SyWier/Bidirectional-Power-Supply/Altium/UPS/ALTIUM_EMBEDDED_MODELS/MLZ1608E100MT.stp

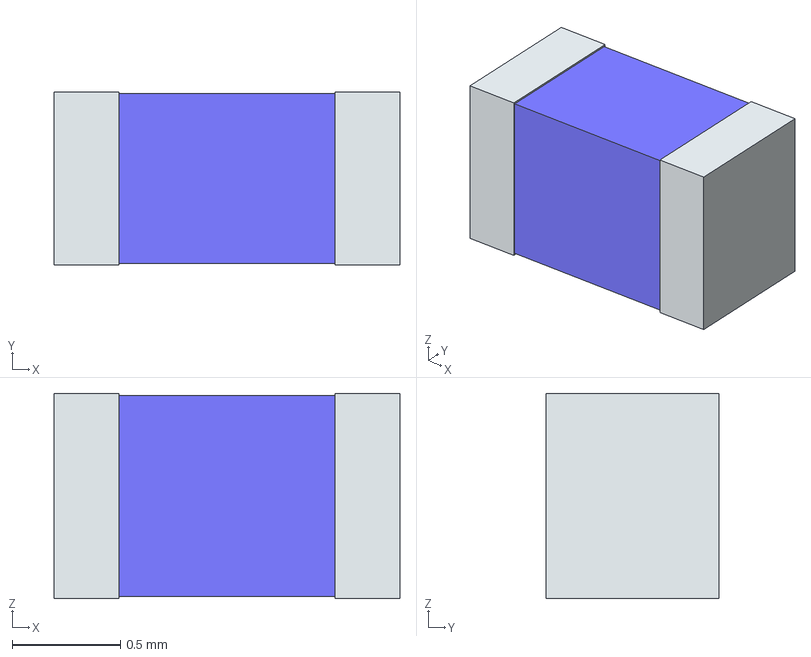
[picture p31: CAD file, 2024-12-01]
Altium/UPS/ALTIUM_EMBEDDED_MODELS/MLZ1608E100MT.stp
1.60 x 0.8 x 0.95 mm
term1
term2
