SyWier/Bidirectional-Power-Supply/Altium/UPS/ALTIUM_EMBEDDED_MODELS/H-LEAD_D10_L12.5__GAS-ESCAPE-RUBBER_COATED-CASE_STRUCTURE.stp

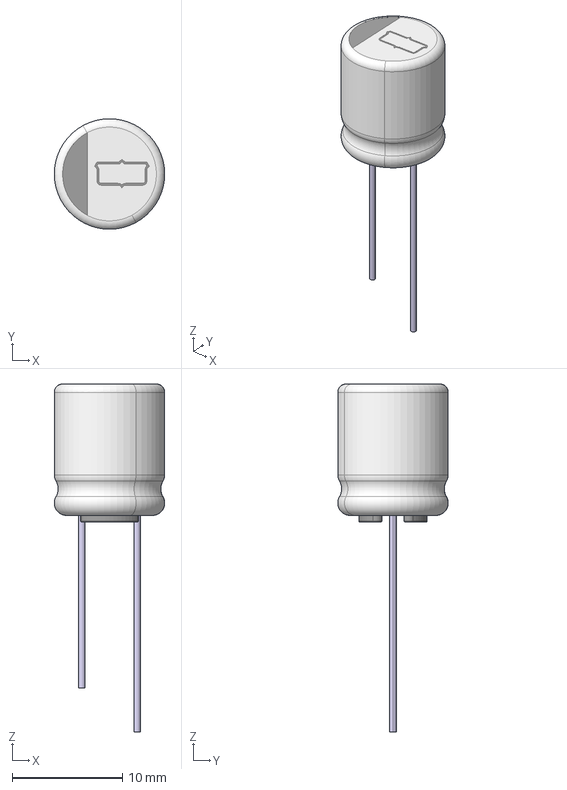
[picture p32: CAD file, 2024-12-01]
Altium/UPS/ALTIUM_EMBEDDED_MODELS/H-LEAD_D10_L12.5__GAS-ESCAPE-RUBBER_COATED-CASE_STRUCTURE.stp
10.00 x 10.00 x 31.5 mm
H-LEAD_D10_TERMINAL+
H-LEAD_D10_TERMINAL-
H-LEAD_D10_L12.5_ELEMENT
