SyWier/Bidirectional-Power-Supply/Altium/UPS/ALTIUM_EMBEDDED_MODELS/LVT12R0050FER.stp

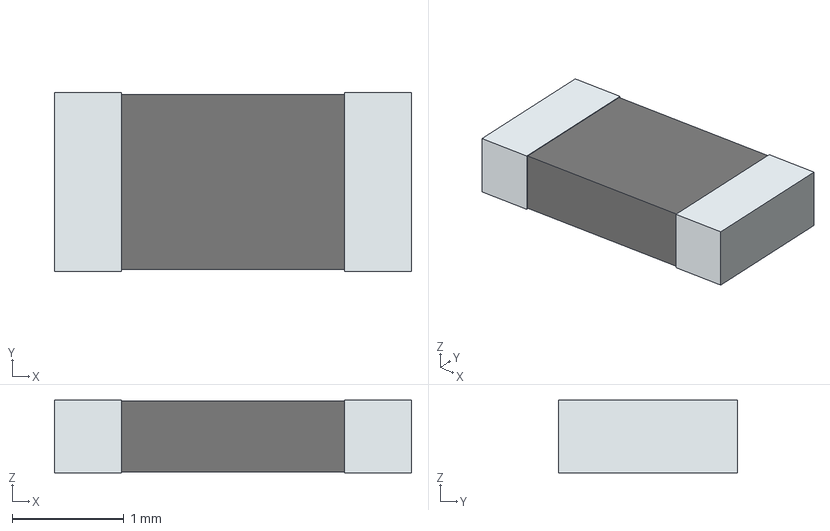
[picture p33: CAD file, 2024-12-01]
Altium/UPS/ALTIUM_EMBEDDED_MODELS/LVT12R0050FER.stp
3.20 x 1.60 x 0.65 mm
term1
term2
