SyWier/Bidirectional-Power-Supply/Altium/UPS/ALTIUM_EMBEDDED_MODELS/PTS526_SMG15J_SMTR2_LFS.stp

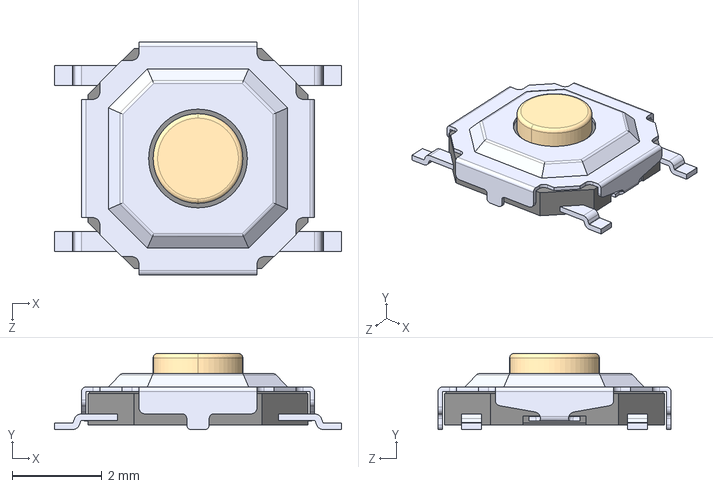
[picture p34: CAD file, 2024-12-01]
Altium/UPS/ALTIUM_EMBEDDED_MODELS/PTS526_SMG15J_SMTR2_LFS.stp
6.40 x 1.70 x 5.20 mm
