SyWier/Bidirectional-Power-Supply/Altium/UPS/ALTIUM_EMBEDDED_MODELS/CP2102N-A02-GQFN20R.stp

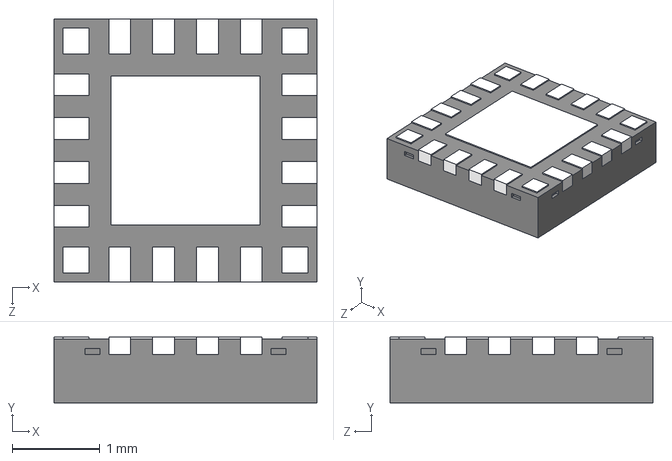
[picture p35: CAD file, 2024-12-01]
Altium/UPS/ALTIUM_EMBEDDED_MODELS/CP2102N-A02-GQFN20R.stp
3.00 x 0.75 x 3.00 mm
