SyWier/Bidirectional-Power-Supply/Altium/UPS/ALTIUM_EMBEDDED_MODELS/TPS2116DRLR.stp

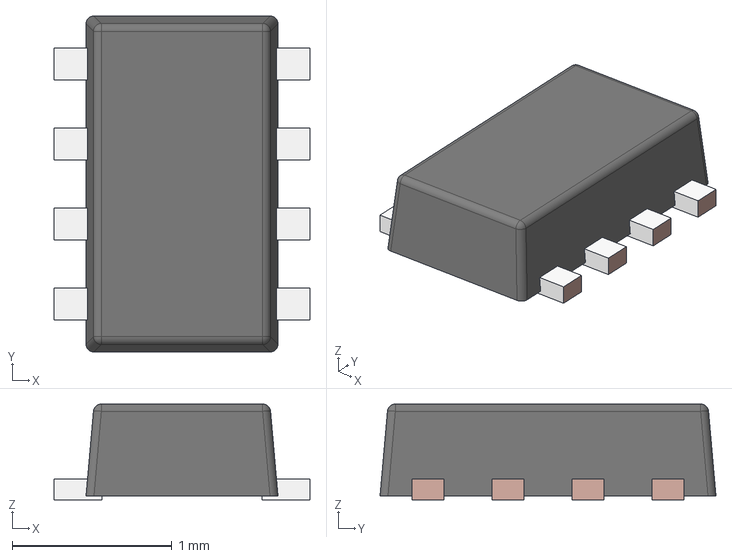
[picture p36: CAD file, 2024-12-01]
Altium/UPS/ALTIUM_EMBEDDED_MODELS/TPS2116DRLR.stp
1.60 x 2.10 x 0.6 mm
FRAME-DRL0008A
BODY-SOT
