SyWier/Bidirectional-Power-Supply/Altium/UPS/ALTIUM_EMBEDDED_MODELS/PHT0603Y1001FGW.stp

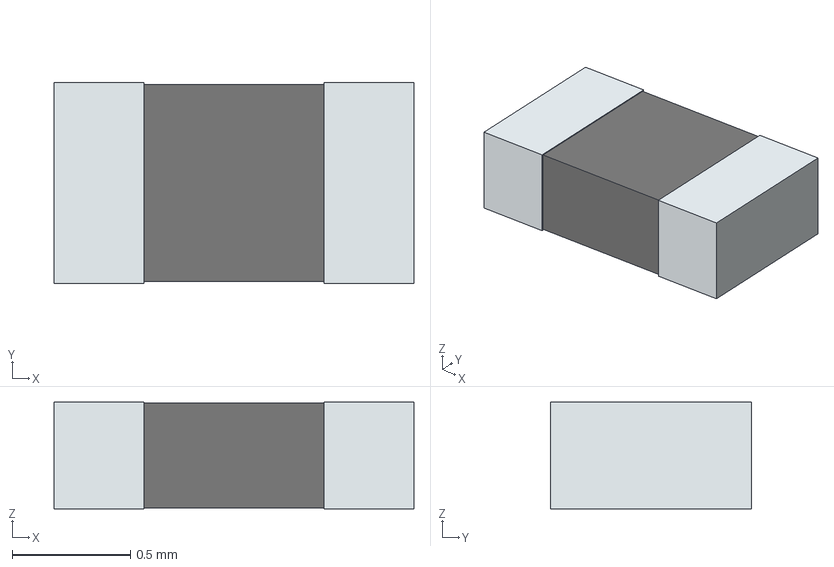
[picture p37: CAD file, 2024-12-01]
Altium/UPS/ALTIUM_EMBEDDED_MODELS/PHT0603Y1001FGW.stp
1.52 x 0.85 x 0.451 mm
term1
term2
