SyWier/Bidirectional-Power-Supply/Altium/UPS/ALTIUM_EMBEDDED_MODELS/MCP6C04T-020E_CHY.stp

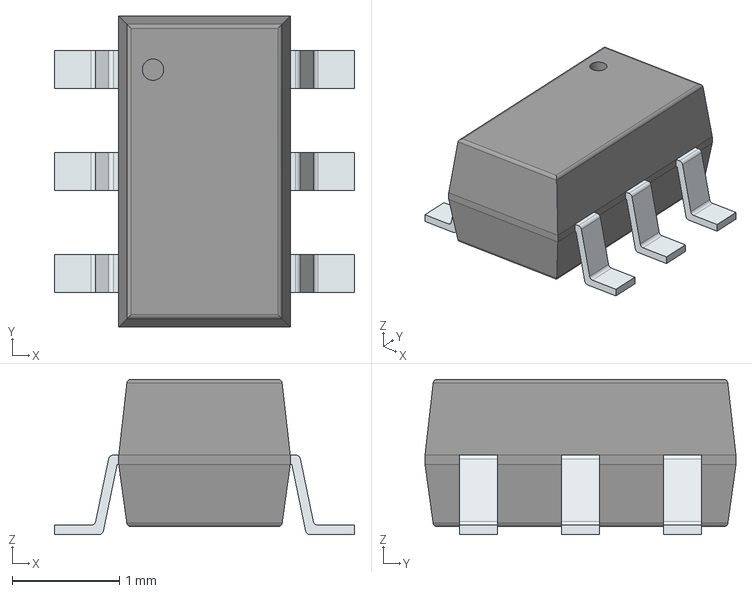
[picture p38: CAD file, 2024-12-01]
Altium/UPS/ALTIUM_EMBEDDED_MODELS/MCP6C04T-020E_CHY.stp
2.80 x 2.90 x 1.45 mm
PinsArrayLR
