SyWier/Bidirectional-Power-Supply/Altium/UPS/ALTIUM_EMBEDDED_MODELS/VS-MBRS130L-M3_5BT.stp

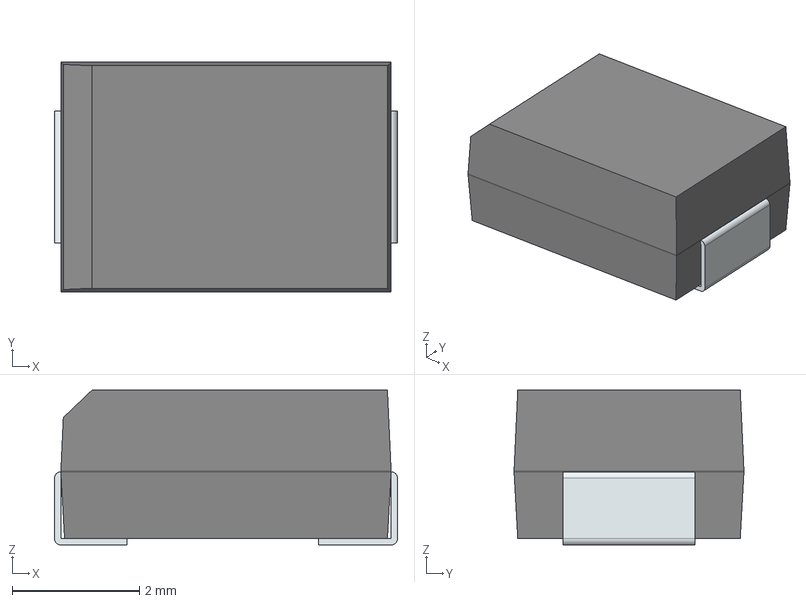
[picture p39: CAD file, 2024-12-01]
Altium/UPS/ALTIUM_EMBEDDED_MODELS/VS-MBRS130L-M3_5BT.stp
5.40 x 3.62 x 2.44 mm
FilletPin1
FilletPin2
