SyWier/Bidirectional-Power-Supply/Altium/UPS/ALTIUM_EMBEDDED_MODELS/ECH8695R-TL-W.stp

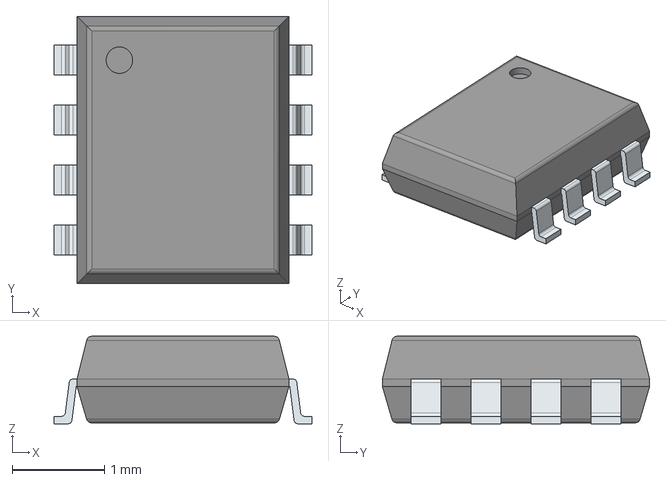
[picture p40: CAD file, 2024-12-01]
Altium/UPS/ALTIUM_EMBEDDED_MODELS/ECH8695R-TL-W.stp
2.80 x 2.90 x 0.95 mm
PinsArrayLR
