SyWier/Bidirectional-Power-Supply/Altium/UPS/ALTIUM_EMBEDDED_MODELS/LP5907QMFX-3.3Q1.stp

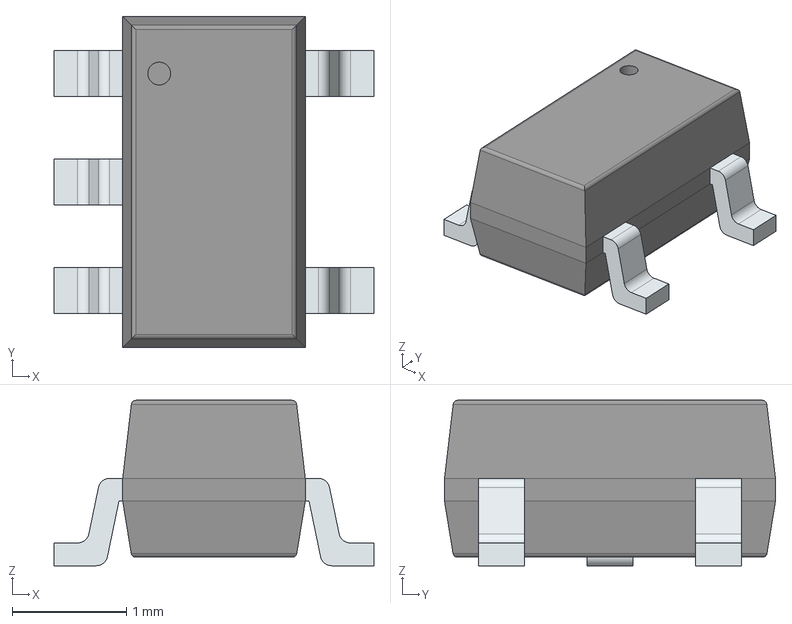
[picture p41: CAD file, 2024-12-01]
Altium/UPS/ALTIUM_EMBEDDED_MODELS/LP5907QMFX-3.3Q1.stp
2.80 x 2.90 x 1.45 mm
PinsArrayL
PinsArrayR
