SyWier/Bidirectional-Power-Supply/Altium/UPS/ALTIUM_EMBEDDED_MODELS/SS-52100-001.stp

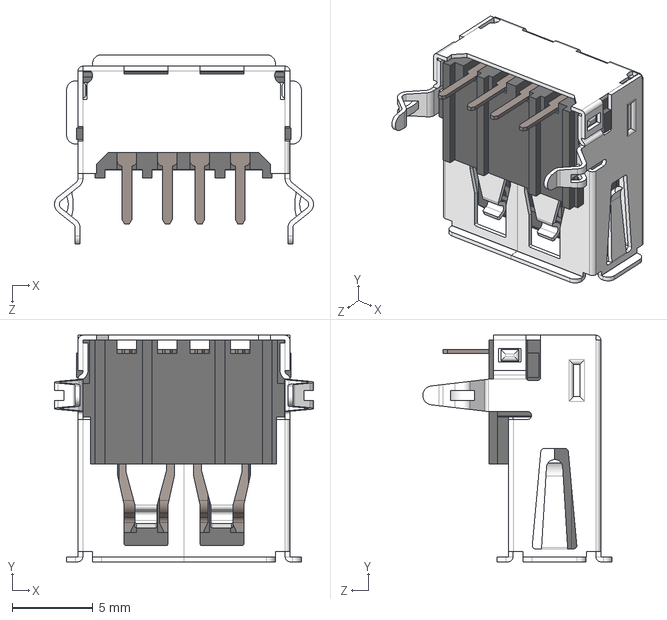
[picture p42: CAD file, 2024-12-01]
Altium/UPS/ALTIUM_EMBEDDED_MODELS/SS-52100-001.stp
16.0 x 14.0 x 11.7 mm
