SyWier/Bidirectional-Power-Supply/Altium/UPS/ALTIUM_EMBEDDED_MODELS/FTSH-105-01-L-DV-K.stp

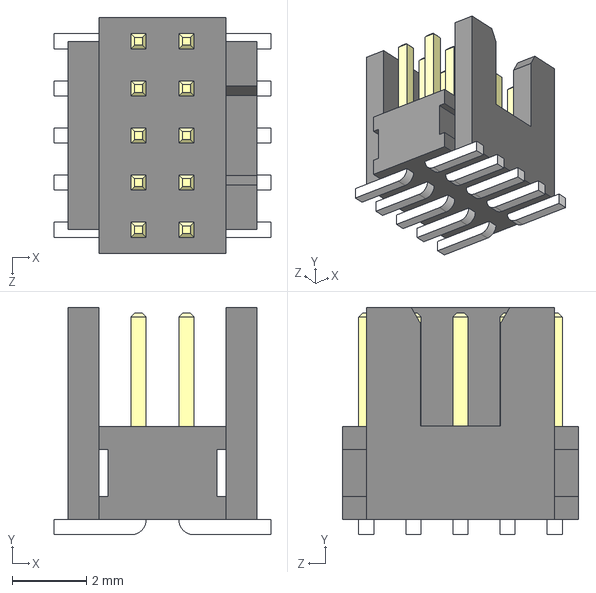
[picture p43: CAD file, 2024-12-01]
Altium/UPS/ALTIUM_EMBEDDED_MODELS/FTSH-105-01-L-DV-K.stp
5.85 x 6.13 x 6.35 mm
