SyWier/Bidirectional-Power-Supply/Altium/UPS/ALTIUM_EMBEDDED_MODELS/USB-B.STEP

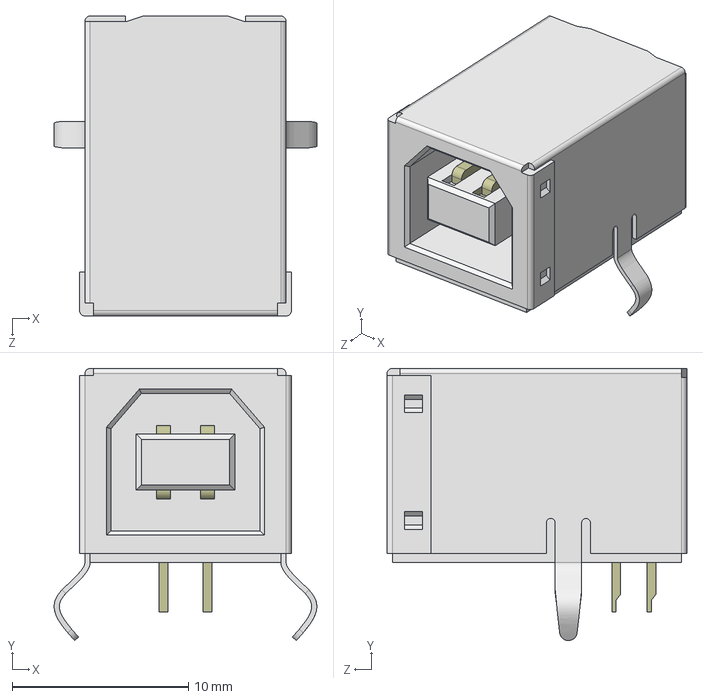
[picture p44: CAD file, 2024-12-01]
Altium/UPS/ALTIUM_EMBEDDED_MODELS/USB-B.STEP
14.9 x 15.4 x 17.0 mm
