SyWier/Bidirectional-Power-Supply/Altium/UPS/ALTIUM_EMBEDDED_MODELS/ESDAULC6-3BP6.stp

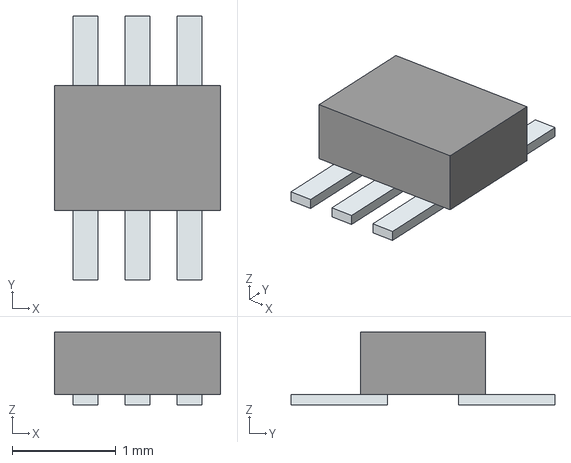
[picture p45: CAD file, 2024-12-01]
Altium/UPS/ALTIUM_EMBEDDED_MODELS/ESDAULC6-3BP6.stp
1.60 x 2.54 x 0.7 mm
Pins
