SyWier/Bidirectional-Power-Supply/CSS/Tools/HiTerm/HiTerm.ini

PORT=COM12
MON_POS=49,635
REN_POS=108,100
WATCHWINDOW_POS=1,0,5,0,0,0,0,0
SETTINGS=2,5,1,2000,10,1,256,0,5,1234,1,40,0,57600
REC_POS_0=30,45
REC_TRIGGER_0_A=0,0,0,1,1
RECTAB_NAME_0_A=Basic
REC_VAR_0_A_0=,1,1000,0,1,1
REC_VAR_0_A_1=,1,1000,0,1,1
REC_VAR_0_A_2=,1,1000,0,1,1
REC_VAR_0_A_3=,1,1000,0,1,1
REC_TRIGGER_0_B=0,0,0,1,1
RECTAB_NAME_0_B=Development
REC_VAR_0_B_0=,1,1000,0,1,1
REC_VAR_0_B_1=,1,1000,0,1,1
REC_VAR_0_B_2=,1,1000,0,1,1
REC_VAR_0_B_3=,1,1000,0,1,1
REC_TRIGGER_0_C=0,0,0,1,1
RECTAB_NAME_0_C=General
REC_VAR_0_C_0=,1,1000,0,1,1
REC_VAR_0_C_1=,1,1000,0,1,1
REC_VAR_0_C_2=,1,1000,0,1,1
REC_VAR_0_C_3=,1,1000,0,1,1
REC_TRIGGER_0_D=0,0,0,1,1
RECTAB_NAME_0_D=Whatever
REC_VAR_0_D_0=,1,1000,0,1,1
REC_VAR_0_D_1=,1,1000,0,1,1
REC_VAR_0_D_2=,1,1000,0,1,1
REC_VAR_0_D_3=,1,1000,0,1,1
REC_TRIGGER_0_E=0,0,0,1,1
RECTAB_NAME_0_E=DbgOsc - 1
REC_VAR_0_E_0=,1,1000,0,1,1
REC_VAR_0_E_1=,1,1000,0,1,1
REC_VAR_0_E_2=,1,1000,0,1,1
REC_VAR_0_E_3=,1,1000,0,1,1
REC_TRIGGER_0_F=0,0,0,1,1
RECTAB_NAME_0_F=DbgOsc - 2
REC_VAR_0_F_0=,1,1000,0,1,1
REC_VAR_0_F_1=,1,1000,0,1,1
REC_VAR_0_F_2=,1,1000,0,1,1
REC_VAR_0_F_3=,1,1000,0,1,1
REC_TRIGGER_0_G=0,0,0,1,1
RECTAB_NAME_0_G=DbgOsc - 3
REC_VAR_0_G_0=,1,1000,0,1,1
REC_VAR_0_G_1=,1,1000,0,1,1
REC_VAR_0_G_2=,1,1000,0,1,1
REC_VAR_0_G_3=,1,1000,0,1,1
REC_TRIGGER_0_H=0,0,0,1,1
RECTAB_NAME_0_H=DbgOsc - 4
REC_VAR_0_H_0=,1,1000,0,1,1
REC_VAR_0_H_1=,1,1000,0,1,1
REC_VAR_0_H_2=,1,1000,0,1,1
REC_VAR_0_H_3=,1,1000,0,1,1
