SyWier/Bidirectional-Power-Supply/CSS/Bootloader/sw280039boot/include/inic.h

/*
 * inic_P.h
 *
 *  Created on: 2019. jún. 21.
 *      Author: Andras Futo
 */

#ifndef INCLUDE_INIC_H_
#define INCLUDE_INIC_H_




#include "F28x_Project.h"
#include "driverlib.h"
#include "device.h"
#include "MUCI.h"
#include "MUCI_recorder.h"


void inic(void);

#endif /* INCLUDE_INIC_H_ */
